yottatsa/apricot-kbd/ref/scans.py

scans = {
	"F1/": [1],
	"F2/": [2],
	"F3/": [3],
	"F4/": [4],
	"F6/": [5],
	"F7/": [6],
	"F8/": [7],
	"F9/": [8],
	"\\": [15],
	"|": [70, 15],
	
	"1": [16],
	"2": [17],
	"3": [18],
	"4": [19],
	"5": [20],
	"6": [21],
	"7": [22],
	"8": [23],
	"9": [24],
	"0": [25],
	"!": [70, 16],
	"@": [70, 17],
	"£": [70, 18],
	"$": [70, 19],
	"%": [70, 20],
	"^": [70, 21],
	"&": [70, 22],
	"*": [70, 23],
	"(": [70, 24],
	")": [70, 25],
	"-": [26],
	"_": [70, 26],
	"=": [27],
	"+": [70, 27],
	"\x7f": [28],
	"\t": [34],
	"q": [35],
	"w": [36],
	"e": [37],
	"r": [38],
	"t": [39],
	"y": [40],
	"u": [41],
	"i": [42],
	"o": [43],
	"p": [44],
	"[": [45],
	"]": [46],
	
	"Q": [70, 35],
	"W": [70, 36],
	"E": [70, 37],
	"R": [70, 38],
	"T": [70, 39],
	"Y": [70, 40],
	"U": [70, 41],
	"I": [70, 42],
	"O": [70, 43],
	"P": [70, 44],
	"{": [70, 45],
	"}": [70, 46],
	
	"a": [53],
	"s": [54],
	"d": [55],
	"f": [56],
	"g": [57],
	"h": [58],
	"j": [59],
	"k": [60],
	"l": [61],
	";": [62],
	"'": [63],
	
	"A": [70, 53],
	"S": [70, 54],
	"D": [70, 55],
	"F": [70, 56],
	"G": [70, 57],
	"H": [70, 58],
	"J": [70, 59],
	"K": [70, 60],
	"L": [70, 61],
	":": [70, 62],
	"\"": [70, 63],
	
	"\n": [64],
	# "LeftShift": [70],
	
	"z": [71],
	"x": [72],
	"c": [73],
	"v": [74],
	"b": [75],
	"n": [76],
	"m": [77],
	",": [78],
	".": [79],
	"/": [80],
	
	"Z": [70, 71],
	"X": [70, 72],
	"C": [70, 73],
	"V": [70, 74],
	"B": [70, 75],
	"N": [70, 76],
	"M": [70, 77],
	"<": [70, 78],
	">": [70, 79],
	"?": [70, 80],
	
	#"RightShift": [81],
	#"Cursorup": [82],
	#"Escape": [87],
	
	#"Left Ctrl": [88],
	" ": [89],
	#"Left": [91],
	#"Down": [92],
	#"Right": [93],

}
